pixawna/cute_step_counter/cad/hardware_reference_NOT_FOR_PRINT/tft_lcd.stl

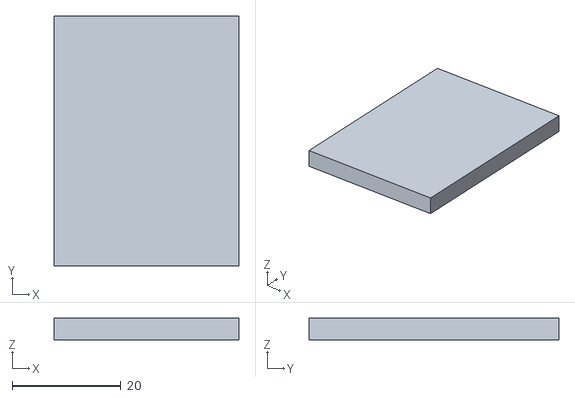
[picture p18: CAD file, 2026-10-04]
cad/hardware_reference_NOT_FOR_PRINT/tft_lcd.stl
34.0 x 46.0 x 4.00
