pixawna/cute_step_counter/fit-check/03_fastener_test.stl

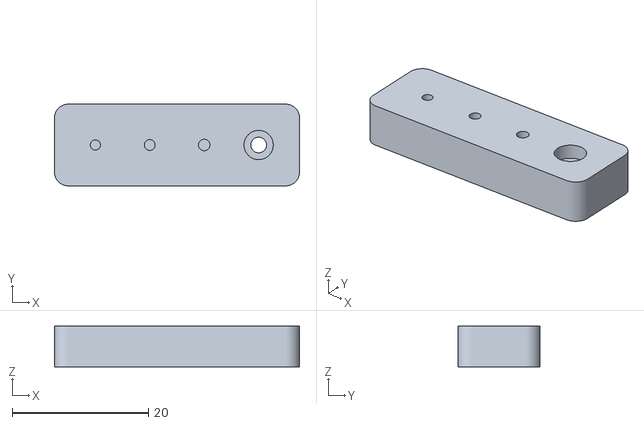
[picture p19: CAD file, 2026-10-04]
fit-check/03_fastener_test.stl
36.0 x 12.0 x 6.00
