pixawna/cute_step_counter/cad/hardware_reference_NOT_FOR_PRINT/sensor_components.stl

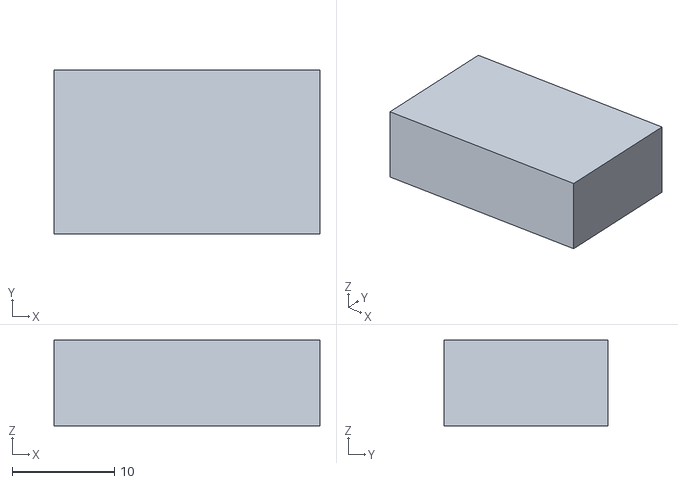
[picture p20: CAD file, 2026-10-04]
cad/hardware_reference_NOT_FOR_PRINT/sensor_components.stl
26.0 x 16.0 x 8.40
