pixawna/cute_step_counter/cad/hardware_reference_NOT_FOR_PRINT/tft_rear_components.stl

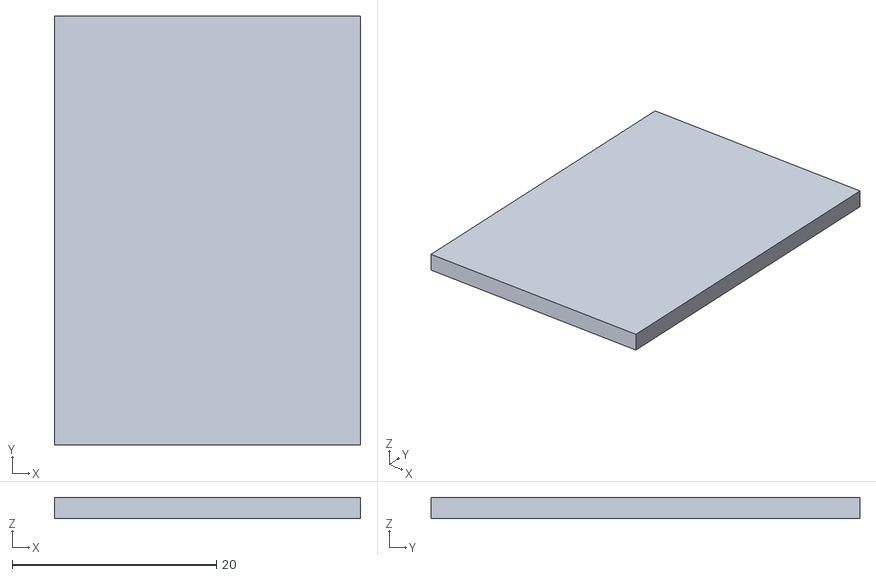
[picture p21: CAD file, 2026-10-04]
cad/hardware_reference_NOT_FOR_PRINT/tft_rear_components.stl
30.0 x 42.0 x 2.10
