pixawna/cute_step_counter/cad/hardware_reference_NOT_FOR_PRINT/tft_pcb.stl

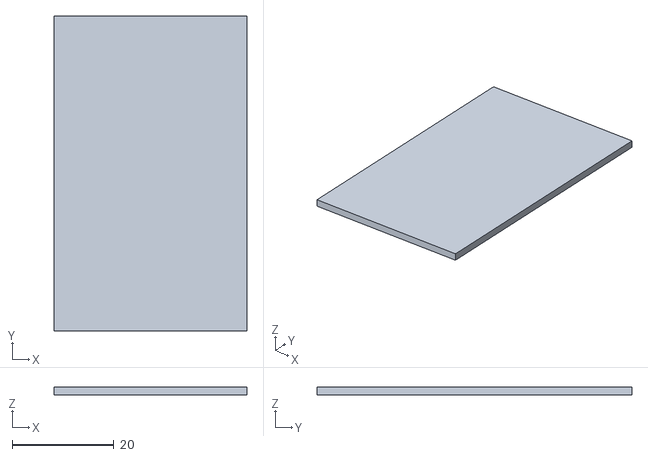
[picture p22: CAD file, 2026-10-04]
cad/hardware_reference_NOT_FOR_PRINT/tft_pcb.stl
38.0 x 62.0 x 1.60
